feichtinger/LEGACY-fingerprint-doorlock/fotos/BILD0145.JPG

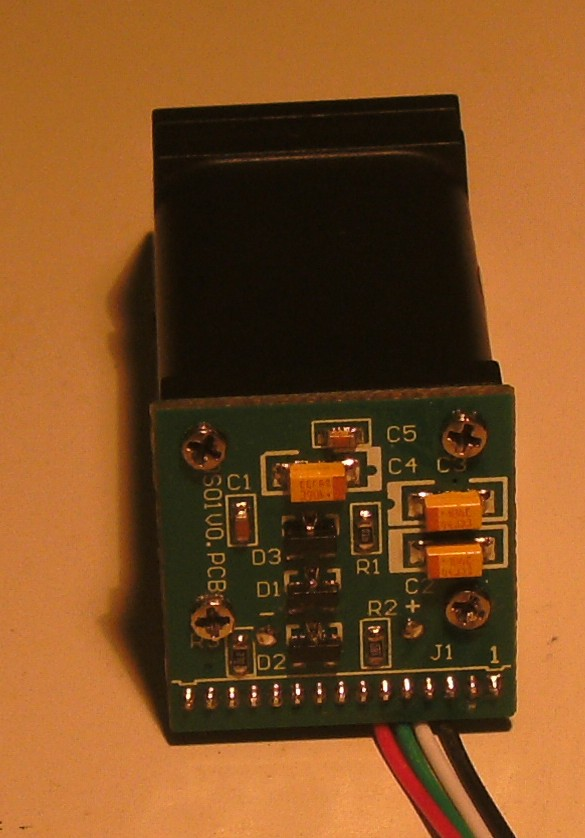
fotos/BILD0145.JPG
