feichtinger/LEGACY-fingerprint-doorlock/fotos/BILD0148.JPG

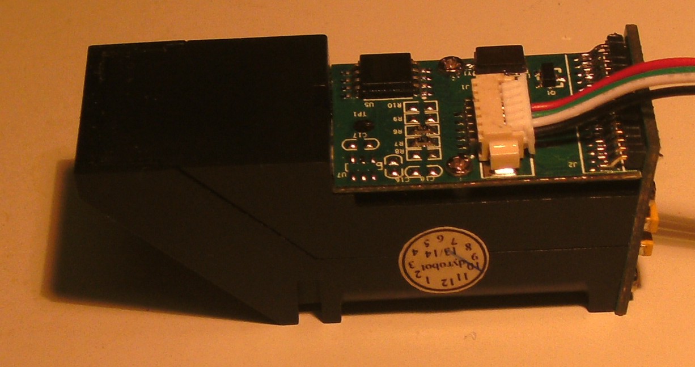
fotos/BILD0148.JPG
