feichtinger/LEGACY-fingerprint-doorlock/fotos/BILD0151.JPG

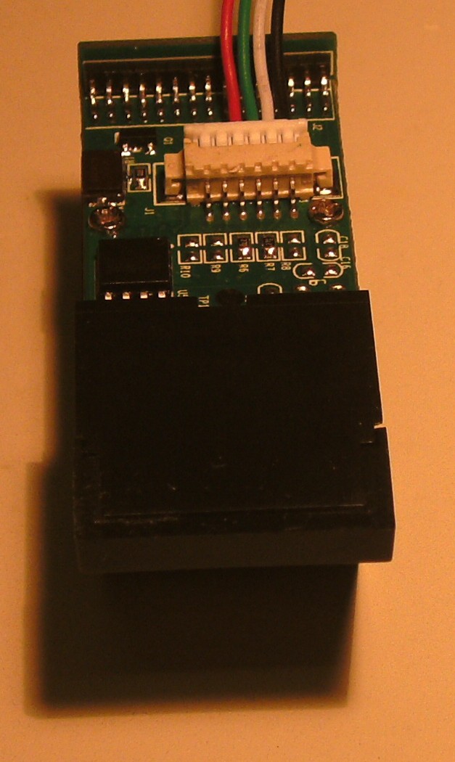
fotos/BILD0151.JPG
