feichtinger/LEGACY-fingerprint-doorlock/fotos/BILD0166.JPG

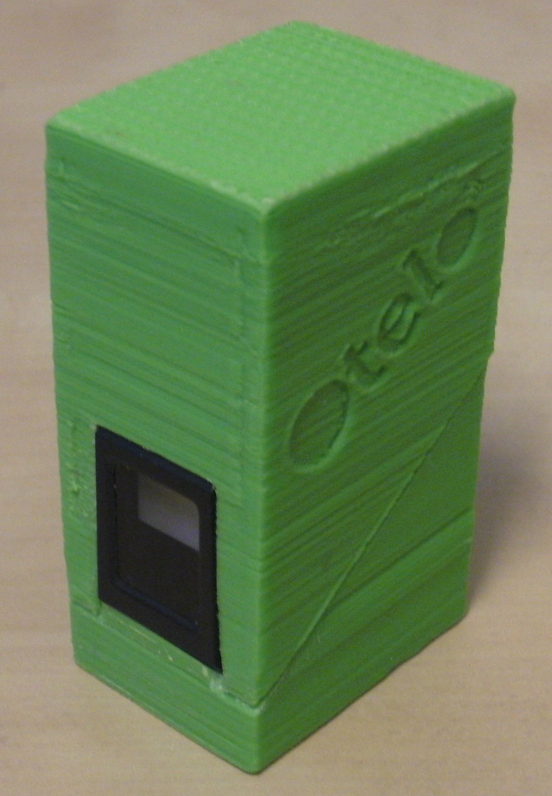
fotos/BILD0166.JPG
