feichtinger/LEGACY-fingerprint-doorlock/fotos/BILD0167.JPG

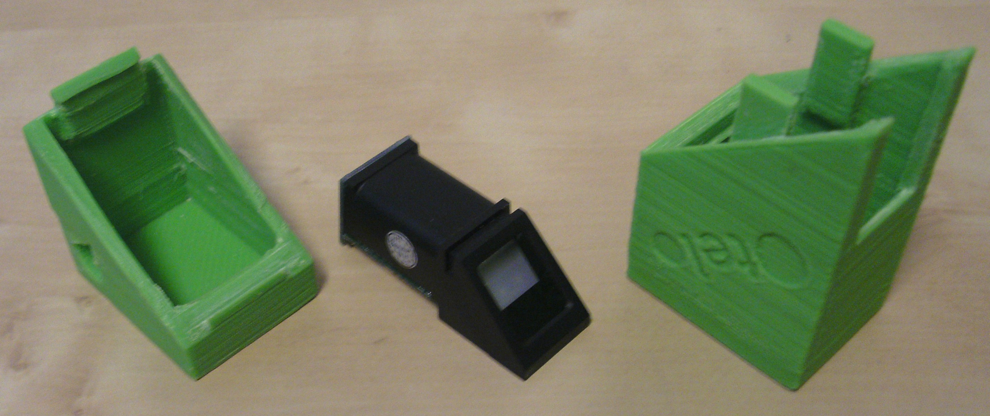
fotos/BILD0167.JPG
