feichtinger/LEGACY-fingerprint-doorlock/housing/rendered/1.png

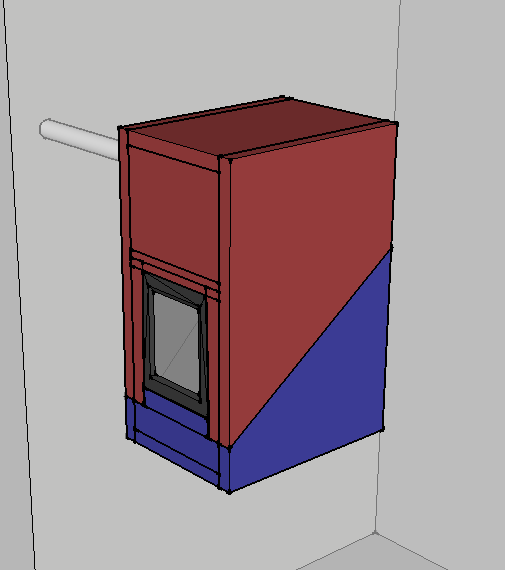
housing/rendered/1.png
