feichtinger/LEGACY-fingerprint-doorlock/housing/rendered/2.png

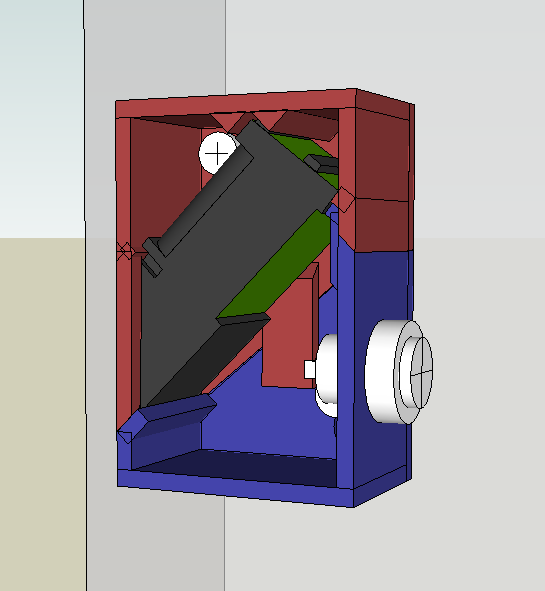
housing/rendered/2.png
