feichtinger/LEGACY-fingerprint-doorlock/housing/rendered/3.png

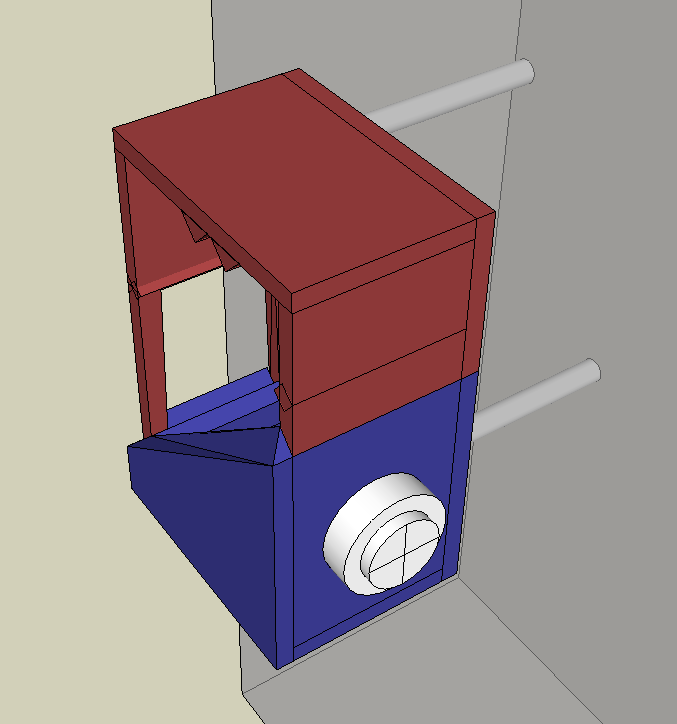
housing/rendered/3.png
