feichtinger/LEGACY-fingerprint-doorlock/housing/rendered/4.png

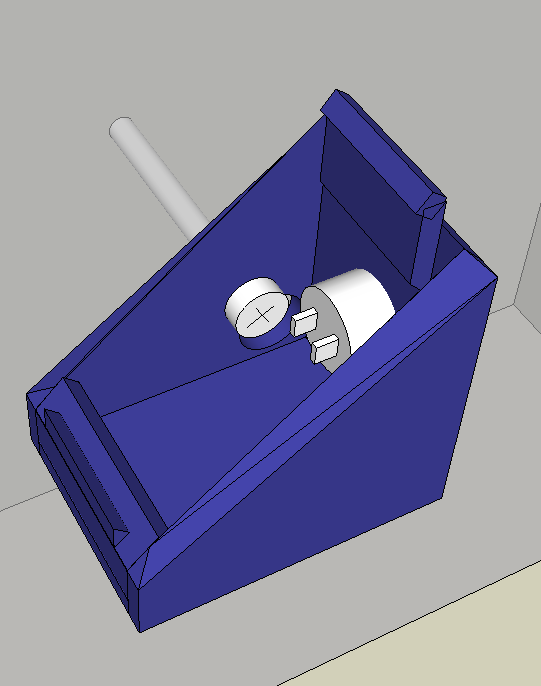
housing/rendered/4.png
