feichtinger/LEGACY-fingerprint-doorlock/housing/rendered/5.png

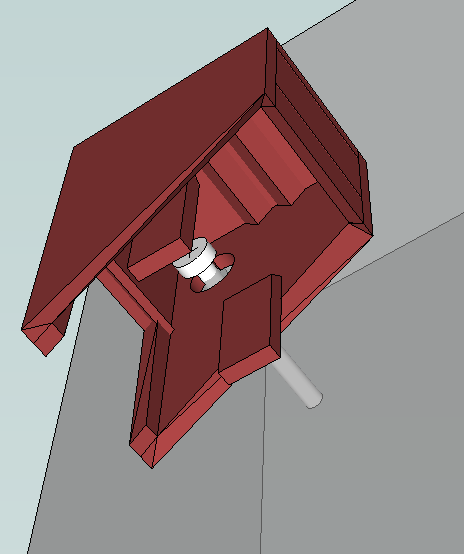
housing/rendered/5.png
