feichtinger/LEGACY-fingerprint-doorlock/housing/rendered/6.png

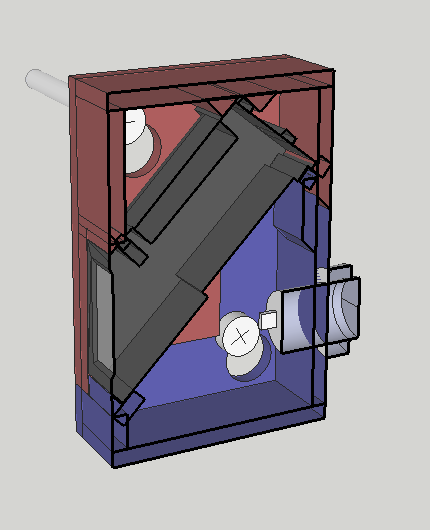
housing/rendered/6.png
