feichtinger/LEGACY-fingerprint-doorlock/housing/rendered/7.png

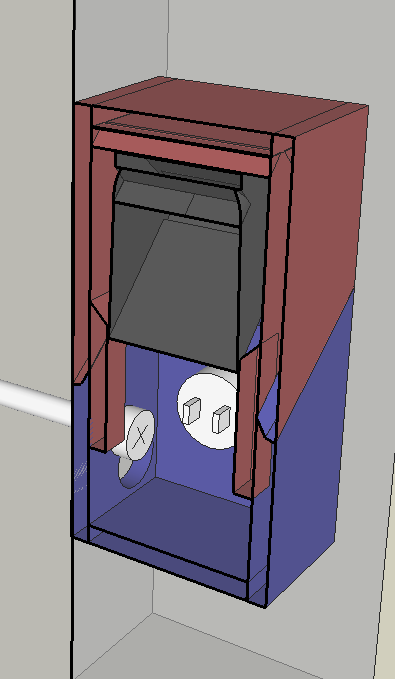
housing/rendered/7.png
